ninjatill/PCB-Capacitive-Touch-Synth/firmware/pcb_touch_synth/system/status_led.h

#pragma once

#include <stdint.h>

enum SystemStatus
{
    SYSTEM_STATUS_BOOTING,
    SYSTEM_STATUS_INITIALIZING,
    SYSTEM_STATUS_OK,
    SYSTEM_STATUS_WARNING,
    SYSTEM_STATUS_FAULT,
    SYSTEM_STATUS_USB_CONNECTED,
    SYSTEM_STATUS_CHARGING,
    SYSTEM_STATUS_RECORDING,
    SYSTEM_STATUS_DEV_ACTIVITY,
    SYSTEM_STATUS_STARTING_AUDIO,
    SYSTEM_STATUS_STARTING_TOUCH,
    SYSTEM_STATUS_MIDI_CONNECTING,  // USB enumeration in progress — fast cyan breathe
    SYSTEM_STATUS_MIDI_ACTIVE       // MIDI mode engaged — solid purple
};

bool status_led_init();
bool status_led_initialized();
void status_led_task();

void status_led_set(SystemStatus status);
SystemStatus status_led_get();
